SamueleFacenda/tiny-reader/src/GxEPD2_213_JD79661.cpp

// GxEPD2 panel class for the JD79661 / EK79029 revision of the Elecrow CrowPanel 2.13" module.
// See the header for the reference sources this is assembled from.
//
// The image path is GxEPD2's epd/GxEPD2_154_M09 (JD79653A, b/w) with two controller
// differences: the previous-frame plane is 0x10 rather than 0x26, and the 0x83 window stands
// on its own, with no 0x91 / 0x92 partial-in / partial-out pair.

#include "GxEPD2_213_JD79661.h"


GxEPD2_213_JD79661::GxEPD2_213_JD79661(int16_t cs, int16_t dc, int16_t rst, int16_t busy) :
  GxEPD2_EPD(cs, dc, rst, busy, LOW, 10000000, WIDTH, HEIGHT, panel, hasColor, hasPartialUpdate, hasFastPartialUpdate),
  _lut_flag(0)
{
}

void GxEPD2_213_JD79661::clearScreen(uint8_t value)
{
  writeScreenBuffer(value);
  refresh(true);
  writeScreenBufferAgain(value);
}

void GxEPD2_213_JD79661::writeScreenBuffer(uint8_t value)
{
  _initial_write = false; // initial full screen buffer clean done
  if (!_using_partial_mode) _Init_Part();
  _writeScreenBuffer(0x13, value); // set current
  if (_initial_refresh) _writeScreenBuffer(0x10, value); // set previous
}

void GxEPD2_213_JD79661::writeScreenBufferAgain(uint8_t value)
{
  if (!_using_partial_mode) _Init_Part();
  _writeScreenBuffer(0x10, value); // set previous
}

void GxEPD2_213_JD79661::_writeScreenBuffer(uint8_t command, uint8_t value)
{
  _writeCommand(command);
  _startTransfer();
  for (uint32_t i = 0; i < uint32_t(WIDTH) * uint32_t(HEIGHT) / 8; i++)
  {
    _transfer(value);
  }
  _endTransfer();
}

void GxEPD2_213_JD79661::writeImage(const uint8_t bitmap[], int16_t x, int16_t y, int16_t w, int16_t h, bool invert, bool mirror_y, bool pgm)
{
  _writeImage(0x13, bitmap, x, y, w, h, invert, mirror_y, pgm);
}

void GxEPD2_213_JD79661::writeImageAgain(const uint8_t bitmap[], int16_t x, int16_t y, int16_t w, int16_t h, bool invert, bool mirror_y, bool pgm)
{
  _writeImage(0x10, bitmap, x, y, w, h, invert, mirror_y, pgm);
}

void GxEPD2_213_JD79661::writeImageToPrevious(const uint8_t bitmap[], int16_t x, int16_t y, int16_t w, int16_t h, bool invert, bool mirror_y, bool pgm)
{
  _writeImage(0x10, bitmap, x, y, w, h, invert, mirror_y, pgm);
}

void GxEPD2_213_JD79661::_writeImage(uint8_t command, const uint8_t bitmap[], int16_t x, int16_t y, int16_t w, int16_t h, bool invert, bool mirror_y, bool pgm)
{
  if (_initial_write) writeScreenBuffer(); // initial full screen buffer clean
  delay(1); // yield() to avoid WDT on ESP8266 and ESP32
  int16_t wb = (w + 7) / 8; // width bytes, bitmaps are padded
  x -= x % 8; // byte boundary
  w = wb * 8; // byte boundary
  int16_t x1 = x < 0 ? 0 : x; // limit
  int16_t y1 = y < 0 ? 0 : y; // limit
  int16_t w1 = x + w < int16_t(WIDTH) ? w : int16_t(WIDTH) - x; // limit
  int16_t h1 = y + h < int16_t(HEIGHT) ? h : int16_t(HEIGHT) - y; // limit
  int16_t dx = x1 - x;
  int16_t dy = y1 - y;
  w1 -= dx;
  h1 -= dy;
  if ((w1 <= 0) || (h1 <= 0)) return;
  if (!_using_partial_mode) _Init_Part();
  _setPartialRamArea(x1, y1, w1, h1);
  _writeCommand(command);
  _startTransfer();
  for (int16_t i = 0; i < h1; i++)
  {
    for (int16_t j = 0; j < w1 / 8; j++)
    {
      uint8_t data;
      // use wb, h of bitmap for index!
      int16_t idx = mirror_y ? j + dx / 8 + ((h - 1 - (i + dy))) * wb : j + dx / 8 + (i + dy) * wb;
      if (pgm)
      {
#if defined(__AVR) || defined(ESP8266) || defined(ESP32)
        data = pgm_read_byte(&bitmap[idx]);
#else
        data = bitmap[idx];
#endif
      }
      else
      {
        data = bitmap[idx];
      }
      if (invert) data = ~data;
      _transfer(data);
    }
  }
  _endTransfer();
  delay(1); // yield() to avoid WDT on ESP8266 and ESP32
}

void GxEPD2_213_JD79661::writeImagePart(const uint8_t bitmap[], int16_t x_part, int16_t y_part, int16_t w_bitmap, int16_t h_bitmap,
                                    int16_t x, int16_t y, int16_t w, int16_t h, bool invert, bool mirror_y, bool pgm)
{
  _writeImagePart(0x13, bitmap, x_part, y_part, w_bitmap, h_bitmap, x, y, w, h, invert, mirror_y, pgm);
}

void GxEPD2_213_JD79661::writeImagePartAgain(const uint8_t bitmap[], int16_t x_part, int16_t y_part, int16_t w_bitmap, int16_t h_bitmap,
    int16_t x, int16_t y, int16_t w, int16_t h, bool invert, bool mirror_y, bool pgm)
{
  _writeImagePart(0x10, bitmap, x_part, y_part, w_bitmap, h_bitmap, x, y, w, h, invert, mirror_y, pgm);
}

void GxEPD2_213_JD79661::writeImagePartToPrevious(const uint8_t bitmap[], int16_t x_part, int16_t y_part, int16_t w_bitmap, int16_t h_bitmap,
    int16_t x, int16_t y, int16_t w, int16_t h, bool invert, bool mirror_y, bool pgm)
{
  _writeImagePart(0x10, bitmap, x_part, y_part, w_bitmap, h_bitmap, x, y, w, h, invert, mirror_y, pgm);
}

void GxEPD2_213_JD79661::_writeImagePart(uint8_t command, const uint8_t bitmap[], int16_t x_part, int16_t y_part, int16_t w_bitmap, int16_t h_bitmap,
                                     int16_t x, int16_t y, int16_t w, int16_t h, bool invert, bool mirror_y, bool pgm)
{
  if (_initial_write) writeScreenBuffer(); // initial full screen buffer clean
  delay(1); // yield() to avoid WDT on ESP8266 and ESP32
  if ((w_bitmap < 0) || (h_bitmap < 0) || (w < 0) || (h < 0)) return;
  if ((x_part < 0) || (x_part >= w_bitmap)) return;
  if ((y_part < 0) || (y_part >= h_bitmap)) return;
  int16_t wb_bitmap = (w_bitmap + 7) / 8; // width bytes, bitmaps are padded
  x_part -= x_part % 8; // byte boundary
  w = w_bitmap - x_part < w ? w_bitmap - x_part : w; // limit
  h = h_bitmap - y_part < h ? h_bitmap - y_part : h; // limit
  x -= x % 8; // byte boundary
  w = 8 * ((w + 7) / 8); // byte boundary, bitmaps are padded
  int16_t x1 = x < 0 ? 0 : x; // limit
  int16_t y1 = y < 0 ? 0 : y; // limit
  int16_t w1 = x + w < int16_t(WIDTH) ? w : int16_t(WIDTH) - x; // limit
  int16_t h1 = y + h < int16_t(HEIGHT) ? h : int16_t(HEIGHT) - y; // limit
  int16_t dx = x1 - x;
  int16_t dy = y1 - y;
  w1 -= dx;
  h1 -= dy;
  if ((w1 <= 0) || (h1 <= 0)) return;
  if (!_using_partial_mode) _Init_Part();
  _setPartialRamArea(x1, y1, w1, h1);
  _writeCommand(command);
  _startTransfer();
  for (int16_t i = 0; i < h1; i++)
  {
    for (int16_t j = 0; j < w1 / 8; j++)
    {
      uint8_t data;
      // use wb_bitmap, h_bitmap of bitmap for index!
      int16_t idx = mirror_y ? x_part / 8 + j + dx / 8 + ((h_bitmap - 1 - (y_part + i + dy))) * wb_bitmap : x_part / 8 + j + dx / 8 + (y_part + i + dy) * wb_bitmap;
      if (pgm)
      {
#if defined(__AVR) || defined(ESP8266) || defined(ESP32)
        data = pgm_read_byte(&bitmap[idx]);
#else
        data = bitmap[idx];
#endif
      }
      else
      {
        data = bitmap[idx];
      }
      if (invert) data = ~data;
      _transfer(data);
    }
  }
  _endTransfer();
  delay(1); // yield() to avoid WDT on ESP8266 and ESP32
}

void GxEPD2_213_JD79661::writeImage(const uint8_t* black, const uint8_t* color, int16_t x, int16_t y, int16_t w, int16_t h, bool invert, bool mirror_y, bool pgm)
{
  if (black)
  {
    writeImage(black, x, y, w, h, invert, mirror_y, pgm);
  }
}

void GxEPD2_213_JD79661::writeImagePart(const uint8_t* black, const uint8_t* color, int16_t x_part, int16_t y_part, int16_t w_bitmap, int16_t h_bitmap,
                                    int16_t x, int16_t y, int16_t w, int16_t h, bool invert, bool mirror_y, bool pgm)
{
  if (black)
  {
    writeImagePart(black, x_part, y_part, w_bitmap, h_bitmap, x, y, w, h, invert, mirror_y, pgm);
  }
}

void GxEPD2_213_JD79661::writeNative(const uint8_t* data1, const uint8_t* data2, int16_t x, int16_t y, int16_t w, int16_t h, bool invert, bool mirror_y, bool pgm)
{
  if (data1)
  {
    writeImage(data1, x, y, w, h, invert, mirror_y, pgm);
  }
}

void GxEPD2_213_JD79661::drawImage(const uint8_t bitmap[], int16_t x, int16_t y, int16_t w, int16_t h, bool invert, bool mirror_y, bool pgm)
{
  writeImage(bitmap, x, y, w, h, invert, mirror_y, pgm);
  refresh(x, y, w, h);
  writeImageAgain(bitmap, x, y, w, h, invert, mirror_y, pgm);
}

void GxEPD2_213_JD79661::drawImagePart(const uint8_t bitmap[], int16_t x_part, int16_t y_part, int16_t w_bitmap, int16_t h_bitmap,
                                   int16_t x, int16_t y, int16_t w, int16_t h, bool invert, bool mirror_y, bool pgm)
{
  writeImagePart(bitmap, x_part, y_part, w_bitmap, h_bitmap, x, y, w, h, invert, mirror_y, pgm);
  refresh(x, y, w, h);
  writeImagePartAgain(bitmap, x_part, y_part, w_bitmap, h_bitmap, x, y, w, h, invert, mirror_y, pgm);
}

void GxEPD2_213_JD79661::drawImage(const uint8_t* black, const uint8_t* color, int16_t x, int16_t y, int16_t w, int16_t h, bool invert, bool mirror_y, bool pgm)
{
  if (black)
  {
    drawImage(black, x, y, w, h, invert, mirror_y, pgm);
  }
}

void GxEPD2_213_JD79661::drawImagePart(const uint8_t* black, const uint8_t* color, int16_t x_part, int16_t y_part, int16_t w_bitmap, int16_t h_bitmap,
                                   int16_t x, int16_t y, int16_t w, int16_t h, bool invert, bool mirror_y, bool pgm)
{
  if (black)
  {
    drawImagePart(black, x_part, y_part, w_bitmap, h_bitmap, x, y, w, h, invert, mirror_y, pgm);
  }
}

void GxEPD2_213_JD79661::drawNative(const uint8_t* data1, const uint8_t* data2, int16_t x, int16_t y, int16_t w, int16_t h, bool invert, bool mirror_y, bool pgm)
{
  if (data1)
  {
    drawImage(data1, x, y, w, h, invert, mirror_y, pgm);
  }
}

void GxEPD2_213_JD79661::refresh(bool partial_update_mode)
{
  if (partial_update_mode) refresh(0, 0, WIDTH, HEIGHT);
  else
  {
    if (_using_partial_mode) _Init_Full();
    _Update_Full();
    _initial_refresh = false; // initial full update done
  }
}

void GxEPD2_213_JD79661::refresh(int16_t x, int16_t y, int16_t w, int16_t h)
{
  if (_initial_refresh) return refresh(false); // initial update needs be full update
  // intersection with screen
  int16_t w1 = x < 0 ? w + x : w; // reduce
  int16_t h1 = y < 0 ? h + y : h; // reduce
  int16_t x1 = x < 0 ? 0 : x; // limit
  int16_t y1 = y < 0 ? 0 : y; // limit
  w1 = x1 + w1 < int16_t(WIDTH) ? w1 : int16_t(WIDTH) - x1; // limit
  h1 = y1 + h1 < int16_t(HEIGHT) ? h1 : int16_t(HEIGHT) - y1; // limit
  if ((w1 <= 0) || (h1 <= 0)) return;
  // make x1, w1 multiple of 8
  w1 += x1 % 8;
  if (w1 % 8 > 0) w1 += 8 - w1 % 8;
  x1 -= x1 % 8;
  bool fullscreen = (x1 == 0) && (y1 == 0) && (w1 == int16_t(WIDTH)) && (h1 == int16_t(HEIGHT));
  if (!_using_partial_mode) _Init_Part();
  _setPartialRamArea(x1, y1, w1, h1, !fullscreen);
  _Update_Part();
}

void GxEPD2_213_JD79661::powerOff(void)
{
  _PowerOff();
}

void GxEPD2_213_JD79661::hibernate()
{
  _PowerOff();
  if (_rst >= 0)
  {
    _writeCommand(0x07); // deep sleep
    _writeData(0xA5);    // check code
    _hibernating = true;
    _init_display_done = false;
  }
}

// The JD79661 addresses a partial window with 0x83, not the UC8151 0x90 / 0x91 / 0x92 trio the
// JD79653A sibling uses. Byte layout and trailing mode flag are from GxEPD2's own JD79661
// driver, epd4c/GxEPD2_213c_GDEY0213F51.
void GxEPD2_213_JD79661::_setPartialRamArea(uint16_t x, uint16_t y, uint16_t w, uint16_t h, bool partial_mode)
{
  uint16_t xe = (x + w - 1) | 0x0007; // byte boundary inclusive (last byte)
  uint16_t ye = y + h - 1;
  x &= 0xFFF8; // byte boundary
  _writeCommand(0x83); // partial window
  _writeData(x / 256);
  _writeData(x % 256);
  _writeData(xe / 256);
  _writeData(xe % 256);
  _writeData(y / 256);
  _writeData(y % 256);
  _writeData(ye / 256);
  _writeData(ye % 256);
  _writeData(partial_mode ? 0x01 : 0x00);
}

// Elecrow's lut_GC() / lut_DU(). 0x20, 0x21 and 0x24 always get their own table; which of 0x22 and
// 0x23 gets which table alternates on every call, to keep VCOM balanced across refreshes.
void GxEPD2_213_JD79661::_writeLut(bool partial)
{
  const unsigned char* lut20 = partial ? lut_20_du : lut_20_gc;
  const unsigned char* lut21 = partial ? lut_21_du : lut_21_gc;
  const unsigned char* lut22 = partial ? lut_22_du : lut_22_gc;
  const unsigned char* lut23 = partial ? lut_23_du : lut_23_gc;
  const unsigned char* lut24 = partial ? lut_24_du : lut_24_gc;
  _writeCommand(0x20);
  _writeDataPGM(lut20, 56);
  _writeCommand(0x21);
  _writeDataPGM(lut21, 56);
  _writeCommand(0x24);
  _writeDataPGM(lut24, 56);
  if (_lut_flag == 0)
  {
    _writeCommand(0x22);
    _writeDataPGM(lut22, 56);
    _writeCommand(0x23);
    _writeDataPGM(lut23, 56);
    _lut_flag = 1;
  }
  else
  {
    _writeCommand(0x22);
    _writeDataPGM(lut23, 56);
    _writeCommand(0x23);
    _writeDataPGM(lut22, 56);
    _lut_flag = 0;
  }
}

void GxEPD2_213_JD79661::_PowerOn()
{
  if (!_power_is_on)
  {
    _writeCommand(0x04);
    _waitWhileBusy("_PowerOn", power_on_time);
  }
  _power_is_on = true;
}

void GxEPD2_213_JD79661::_PowerOff()
{
  if (_power_is_on)
  {
    _writeCommand(0x02); // power off
    _writeData(0x00);
    _waitWhileBusy("_PowerOff", power_off_time);
  }
  _power_is_on = false;
  _using_partial_mode = false;
}

void GxEPD2_213_JD79661::_InitDisplay()
{
  if (_hibernating) _reset();
  // Verbatim from Elecrow's EPD_Init(), example/arduino-v1.2/main/EPD_Init.cpp.
  _writeCommand(0x00); // PSR, panel setting
  // bit3 gate scan direction, bit2 source shift direction; 0xF3 / 0xF7 / 0xFB / 0xFF are the
  // four combinations. Elecrow's value, kept deliberately: the panel renders mirrored left to
  // right this way, and the mirror is undone by GxEPD2::GDE0213B1 / _reverse (see the header).
  // Do not flip bit3 to un-mirror it — that moves the gate origin while GxEPD2's partial
  // windows keep addressing the old end, corrupting every partial refresh.
  _writeData(0xF7);
  _writeData(0x8A);
  _writeCommand(0x01); // PWR, power setting
  _writeData(0x03);
  _writeData(0x00);
  _writeData(0x3F);
  _writeData(0x3F);
  _writeData(0x03);
  _writeCommand(0x03); // POFS
  _writeData(0x00);
  _writeCommand(0x06); // BTST, booster soft start
  _writeData(0x27);
  _writeData(0x27);
  _writeData(0x2F);
  _writeCommand(0x30); // PLL control
  _writeData(0x0D);
  _writeCommand(0x60); // TCON
  _writeData(0x22);
  _writeCommand(0x82); // VDCS, VCOM DC setting
  _writeData(0x07);
  _writeCommand(0xE3); // PWS, power saving
  _writeData(0x88);
  _writeCommand(0x41);
  _writeData(0x00);
  // TRES. Three bytes, as the b/w JD796xx panels want, not the four the 4-colour F51 sends.
  _writeCommand(0x61);
  _writeData(WIDTH);
  _writeData(HEIGHT / 256);
  _writeData(HEIGHT % 256);
  _writeCommand(0x65); // gate / source start offsets
  _writeData(0x00);
  _writeData(0x00);
  _writeData(0x00);
  _writeCommand(0x50); // CDI, VCOM and data interval
  _writeData(0xB7);
  _init_display_done = true;
}

void GxEPD2_213_JD79661::_Init_Full()
{
  _InitDisplay();
  _writeCommand(0x50); // CDI, as Elecrow sets it immediately before image data
  _writeData(0xD7);
  _PowerOn();
  _using_partial_mode = false;
}

void GxEPD2_213_JD79661::_Init_Part()
{
  _InitDisplay();
  _writeCommand(0x50);
  _writeData(0xD7);
  _PowerOn();
  _using_partial_mode = true;
}

// The waveform download belongs here rather than in _Init_*, so the 0x22 / 0x23 alternation
// advances once per refresh.
//
// 0x17 / 0xA5 is Elecrow's refresh opcode for this module, and is likely an auto sequence
// (power on, refresh, power off), hence clearing _power_is_on afterwards: a redundant 0x04 on
// the next refresh is harmless, a missing one is a dead refresh.
void GxEPD2_213_JD79661::_Update_Full()
{
  _writeLut(false);
  _writeCommand(0x17);
  _writeData(0xA5);
  _waitWhileBusy("_Update_Full", full_refresh_time);
  _power_is_on = false;
}

void GxEPD2_213_JD79661::_Update_Part()
{
  _writeLut(true);
  _writeCommand(0x17);
  _writeData(0xA5);
  _waitWhileBusy("_Update_Part", partial_refresh_time);
  _power_is_on = false;
}

// Waveform tables, copied byte for byte from Elecrow's EPD_Init.cpp. GC is the full-refresh
// waveform, DU the partial one. 56 bytes each, of which only the first 8 are non-zero; the
// tail is sent anyway, as the controller expects 56.

const unsigned char GxEPD2_213_JD79661::lut_20_gc[] PROGMEM =
{
  0x01, 0x00, 0x14, 0x14, 0x01, 0x00, 0x00, 0x01,
  0x00, 0x00, 0x00, 0x00, 0x00, 0x00, 0x00, 0x00,
  0x00, 0x00, 0x00, 0x00, 0x00, 0x00, 0x00, 0x00,
  0x00, 0x00, 0x00, 0x00, 0x00, 0x00, 0x00, 0x00,
  0x00, 0x00, 0x00, 0x00, 0x00, 0x00, 0x00, 0x00,
  0x00, 0x00, 0x00, 0x00, 0x00, 0x00, 0x00, 0x00,
  0x00, 0x00, 0x00, 0x00, 0x00, 0x00, 0x00, 0x00,
};

const unsigned char GxEPD2_213_JD79661::lut_20_du[] PROGMEM =
{
  0x01, 0x00, 0x14, 0x01, 0x01, 0x00, 0x00, 0x00,
  0x00, 0x00, 0x00, 0x00, 0x00, 0x00, 0x00, 0x00,
  0x00, 0x00, 0x00, 0x00, 0x00, 0x00, 0x00, 0x00,
  0x00, 0x00, 0x00, 0x00, 0x00, 0x00, 0x00, 0x00,
  0x00, 0x00, 0x00, 0x00, 0x00, 0x00, 0x00, 0x00,
  0x00, 0x00, 0x00, 0x00, 0x00, 0x00, 0x00, 0x00,
  0x00, 0x00, 0x00, 0x00, 0x00, 0x00, 0x00, 0x00,
};

const unsigned char GxEPD2_213_JD79661::lut_21_gc[] PROGMEM =
{
  0x01, 0x60, 0x14, 0x14, 0x01, 0x00, 0x00, 0x01,
  0x00, 0x00, 0x00, 0x00, 0x00, 0x00, 0x00, 0x00,
  0x00, 0x00, 0x00, 0x00, 0x00, 0x00, 0x00, 0x00,
  0x00, 0x00, 0x00, 0x00, 0x00, 0x00, 0x00, 0x00,
  0x00, 0x00, 0x00, 0x00, 0x00, 0x00, 0x00, 0x00,
  0x00, 0x00, 0x00, 0x00, 0x00, 0x00, 0x00, 0x00,
  0x00, 0x00, 0x00, 0x00, 0x00, 0x00, 0x00, 0x00,
};

const unsigned char GxEPD2_213_JD79661::lut_21_du[] PROGMEM =
{
  0x01, 0x00, 0x14, 0x01, 0x01, 0x00, 0x00, 0x00,
  0x00, 0x00, 0x00, 0x00, 0x00, 0x00, 0x00, 0x00,
  0x00, 0x00, 0x00, 0x00, 0x00, 0x00, 0x00, 0x00,
  0x00, 0x00, 0x00, 0x00, 0x00, 0x00, 0x00, 0x00,
  0x00, 0x00, 0x00, 0x00, 0x00, 0x00, 0x00, 0x00,
  0x00, 0x00, 0x00, 0x00, 0x00, 0x00, 0x00, 0x00,
  0x00, 0x00, 0x00, 0x00, 0x00, 0x00, 0x00, 0x00,
};

const unsigned char GxEPD2_213_JD79661::lut_22_gc[] PROGMEM =
{
  0x01, 0x20, 0x14, 0x14, 0x01, 0x00, 0x00, 0x01,
  0x00, 0x00, 0x00, 0x00, 0x00, 0x00, 0x00, 0x00,
  0x00, 0x00, 0x00, 0x00, 0x00, 0x00, 0x00, 0x00,
  0x00, 0x00, 0x00, 0x00, 0x00, 0x00, 0x00, 0x00,
  0x00, 0x00, 0x00, 0x00, 0x00, 0x00, 0x00, 0x00,
  0x00, 0x00, 0x00, 0x00, 0x00, 0x00, 0x00, 0x00,
  0x00, 0x00, 0x00, 0x00, 0x00, 0x00, 0x00, 0x00,
};

const unsigned char GxEPD2_213_JD79661::lut_22_du[] PROGMEM =
{
  0x01, 0x80, 0x14, 0x01, 0x01, 0x00, 0x00, 0x00,
  0x00, 0x00, 0x00, 0x00, 0x00, 0x00, 0x00, 0x00,
  0x00, 0x00, 0x00, 0x00, 0x00, 0x00, 0x00, 0x00,
  0x00, 0x00, 0x00, 0x00, 0x00, 0x00, 0x00, 0x00,
  0x00, 0x00, 0x00, 0x00, 0x00, 0x00, 0x00, 0x00,
  0x00, 0x00, 0x00, 0x00, 0x00, 0x00, 0x00, 0x00,
  0x00, 0x00, 0x00, 0x00, 0x00, 0x00, 0x00, 0x00,
};

const unsigned char GxEPD2_213_JD79661::lut_23_gc[] PROGMEM =
{
  0x01, 0x10, 0x14, 0x14, 0x01, 0x00, 0x00, 0x01,
  0x00, 0x00, 0x00, 0x00, 0x00, 0x00, 0x00, 0x00,
  0x00, 0x00, 0x00, 0x00, 0x00, 0x00, 0x00, 0x00,
  0x00, 0x00, 0x00, 0x00, 0x00, 0x00, 0x00, 0x00,
  0x00, 0x00, 0x00, 0x00, 0x00, 0x00, 0x00, 0x00,
  0x00, 0x00, 0x00, 0x00, 0x00, 0x00, 0x00, 0x00,
  0x00, 0x00, 0x00, 0x00, 0x00, 0x00, 0x00, 0x00,
};

const unsigned char GxEPD2_213_JD79661::lut_23_du[] PROGMEM =
{
  0x01, 0x40, 0x14, 0x01, 0x01, 0x00, 0x00, 0x00,
  0x00, 0x00, 0x00, 0x00, 0x00, 0x00, 0x00, 0x00,
  0x00, 0x00, 0x00, 0x00, 0x00, 0x00, 0x00, 0x00,
  0x00, 0x00, 0x00, 0x00, 0x00, 0x00, 0x00, 0x00,
  0x00, 0x00, 0x00, 0x00, 0x00, 0x00, 0x00, 0x00,
  0x00, 0x00, 0x00, 0x00, 0x00, 0x00, 0x00, 0x00,
  0x00, 0x00, 0x00, 0x00, 0x00, 0x00, 0x00, 0x00,
};

const unsigned char GxEPD2_213_JD79661::lut_24_gc[] PROGMEM =
{
  0x01, 0x90, 0x14, 0x14, 0x01, 0x00, 0x00, 0x01,
  0x00, 0x00, 0x00, 0x00, 0x00, 0x00, 0x00, 0x00,
  0x00, 0x00, 0x00, 0x00, 0x00, 0x00, 0x00, 0x00,
  0x00, 0x00, 0x00, 0x00, 0x00, 0x00, 0x00, 0x00,
  0x00, 0x00, 0x00, 0x00, 0x00, 0x00, 0x00, 0x00,
  0x00, 0x00, 0x00, 0x00, 0x00, 0x00, 0x00, 0x00,
  0x00, 0x00, 0x00, 0x00, 0x00, 0x00, 0x00, 0x00,
};

const unsigned char GxEPD2_213_JD79661::lut_24_du[] PROGMEM =
{
  0x01, 0x00, 0x14, 0x01, 0x01, 0x00, 0x00, 0x00,
  0x00, 0x00, 0x00, 0x00, 0x00, 0x00, 0x00, 0x00,
  0x00, 0x00, 0x00, 0x00, 0x00, 0x00, 0x00, 0x00,
  0x00, 0x00, 0x00, 0x00, 0x00, 0x00, 0x00, 0x00,
  0x00, 0x00, 0x00, 0x00, 0x00, 0x00, 0x00, 0x00,
  0x00, 0x00, 0x00, 0x00, 0x00, 0x00, 0x00, 0x00,
  0x00, 0x00, 0x00, 0x00, 0x00, 0x00, 0x00, 0x00,
};
